Pollyyaooo/515_monopoly/hardware/vision_archi/摄像头8.stl

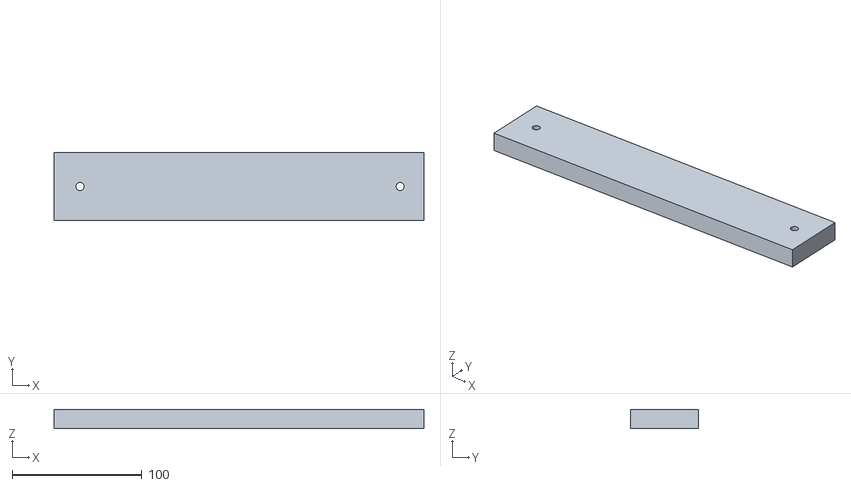
[picture p41: CAD file, 2026-06-08]
hardware/vision_archi/摄像头8.stl
285.0 x 52.0 x 15.0
