Pollyyaooo/515_monopoly/test/Hall Effect test/src/main.cpp

#include <Arduino.h>

void printSensorStatus(int pin, String name) {
  int val = analogRead(pin);
  float voltage = val * 3.3 / 4095.0;

  Serial.print(name);
  Serial.print(" | Voltage: ");
  Serial.print(voltage, 3);
  Serial.print("V  →  ");

  if (voltage > 2.5) {
    Serial.println("玩家A 到达！");
  } else if (voltage < 0.8) {
    Serial.println("玩家B 到达！");
  } else {
    Serial.println("空格");
  }
}

void setup() {
  Serial.begin(115200);
}

void loop() {
  printSensorStatus(A0, "Sensor1");
  printSensorStatus(A1, "Sensor2");
  Serial.println("---");
  delay(500);
}
